jasontsemf/OptiMice/Optimice_V2/Eagle/optiMiceV2/export/board/optiMiceV2_6.png

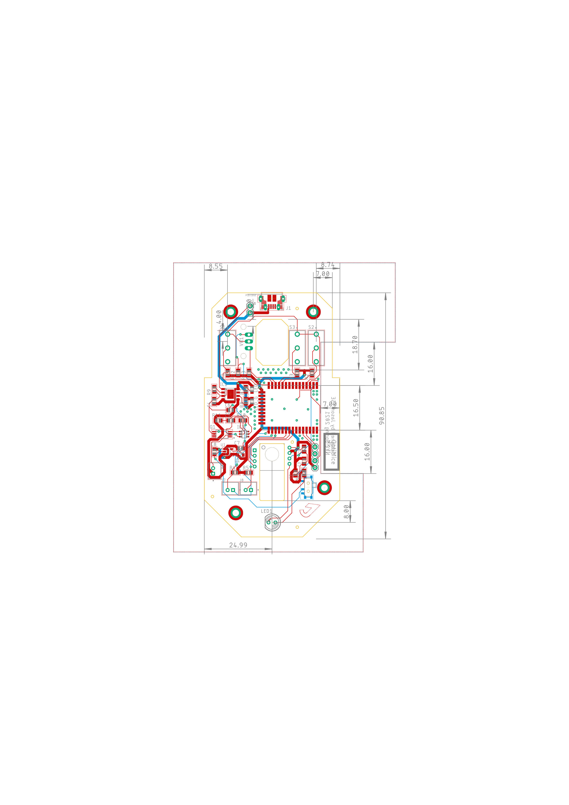
Optimice_V2/Eagle/optiMiceV2/export/board/optiMiceV2_6.png
