jasontsemf/OptiMice/Optimice_V2/Eagle/optiMiceV2/export/board/optiMiceV2_6_bottom.png

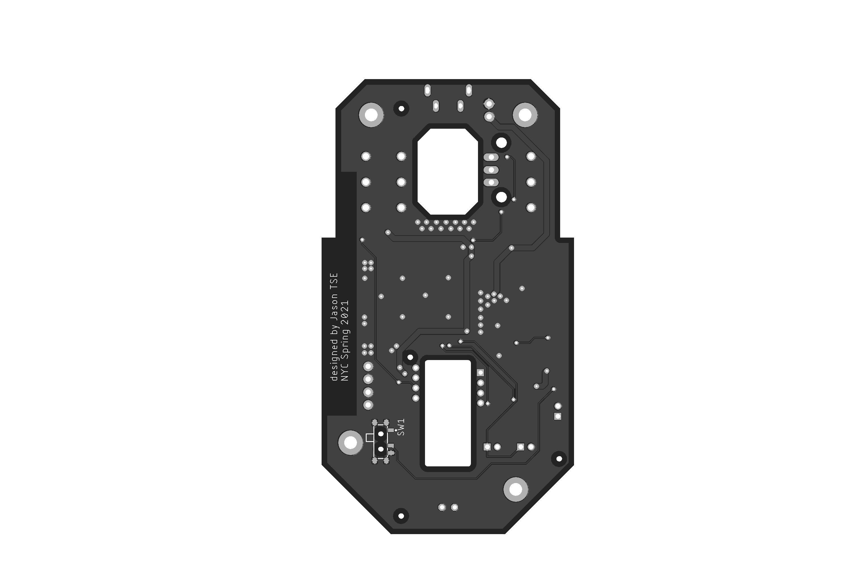
Optimice_V2/Eagle/optiMiceV2/export/board/optiMiceV2_6_bottom.png
