jasontsemf/OptiMice/Optimice_V2/Eagle/optiMiceV2/export/drawing/optiMiceV2_blocktitle.png

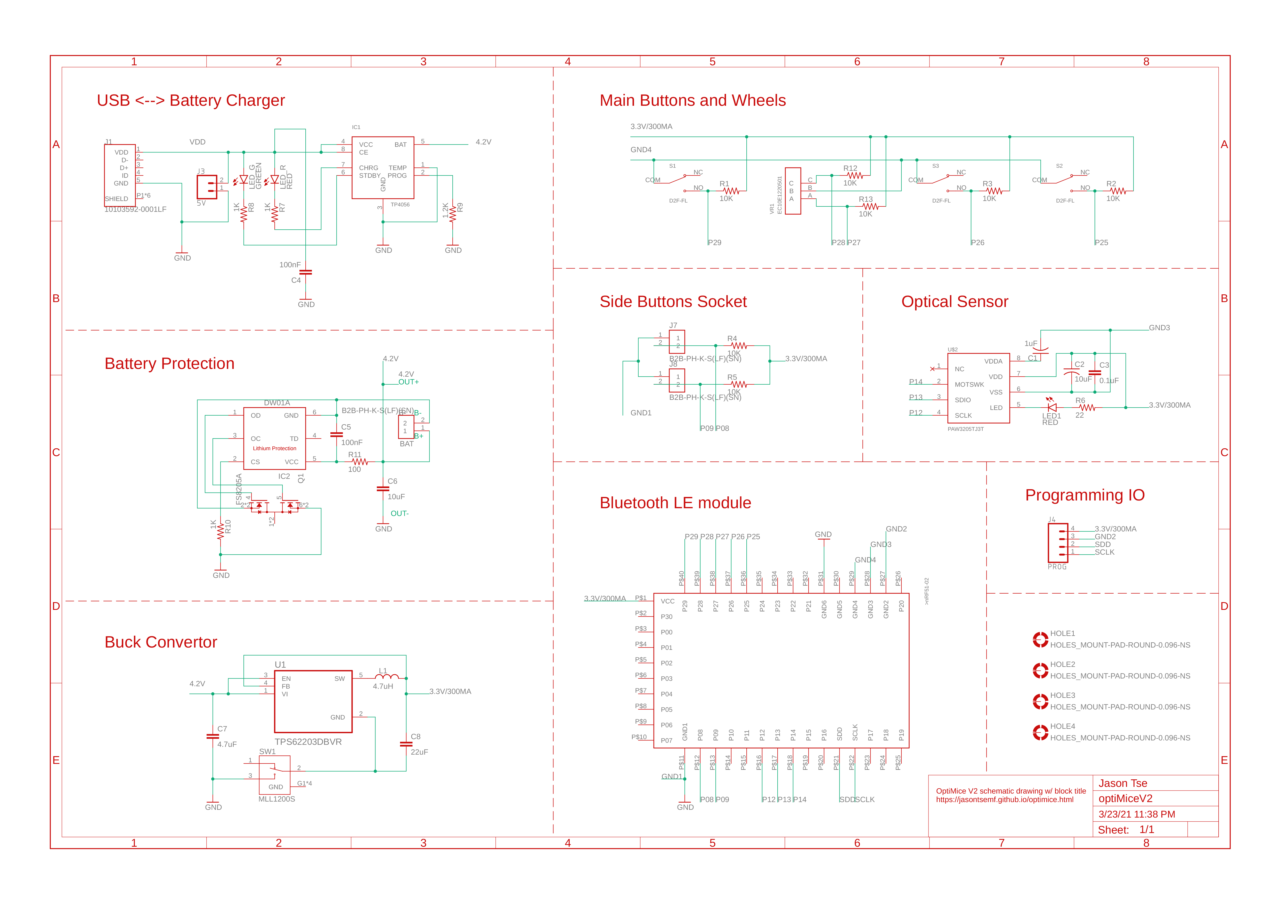
Optimice_V2/Eagle/optiMiceV2/export/drawing/optiMiceV2_blocktitle.png
