jasontsemf/OptiMice/Optimice_V2/Eagle/optiMiceV2/export/drawing/wrong/optiMiceV2_drawing_v0.1.png

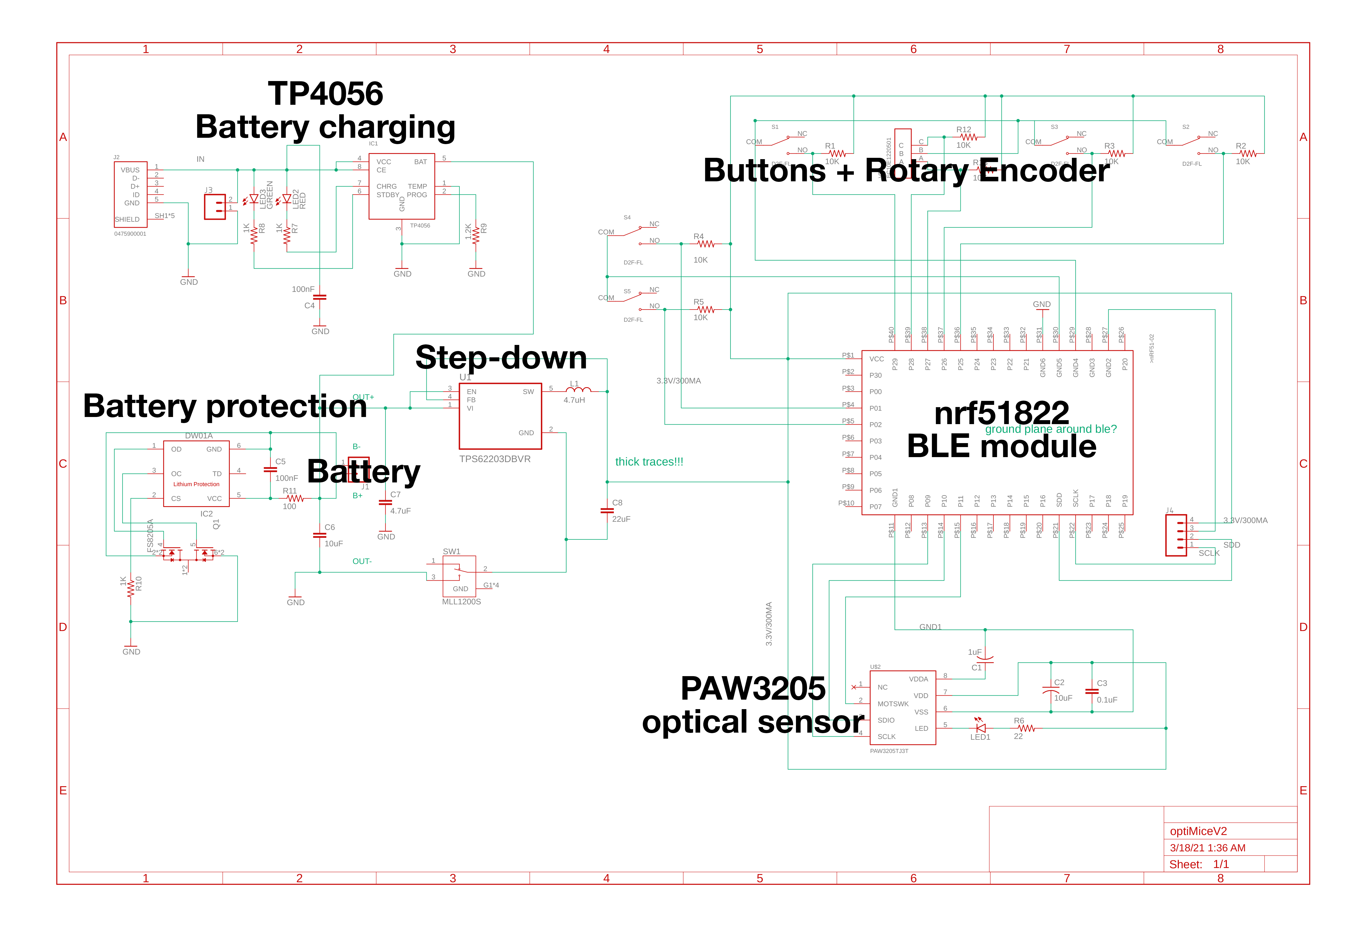
Optimice_V2/Eagle/optiMiceV2/export/drawing/wrong/optiMiceV2_drawing_v0.1.png
