jasontsemf/OptiMice/Optimice_V2/Eagle/optiMiceV2/export/isometric/Layer 2.png

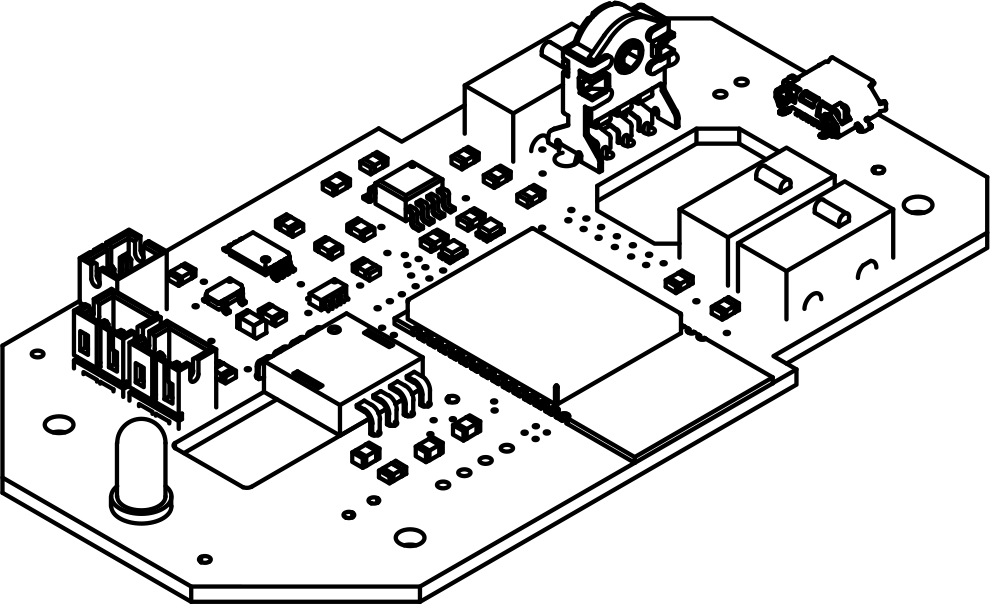
Optimice_V2/Eagle/optiMiceV2/export/isometric/Layer 2.png
