jasontsemf/OptiMice/Optimice_V2/img/_DSC0003.JPG

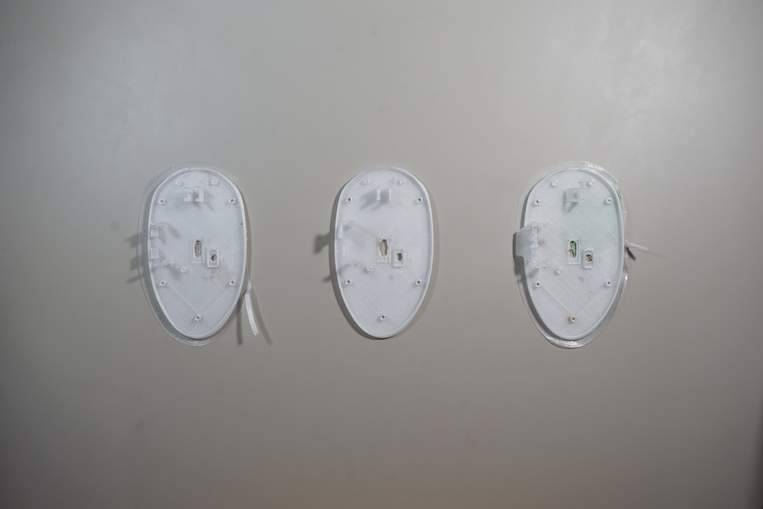
Optimice_V2/img/_DSC0003.JPG
