jasontsemf/OptiMice/Optimice_V2/img/IMG_20210307_201544_508.jpg

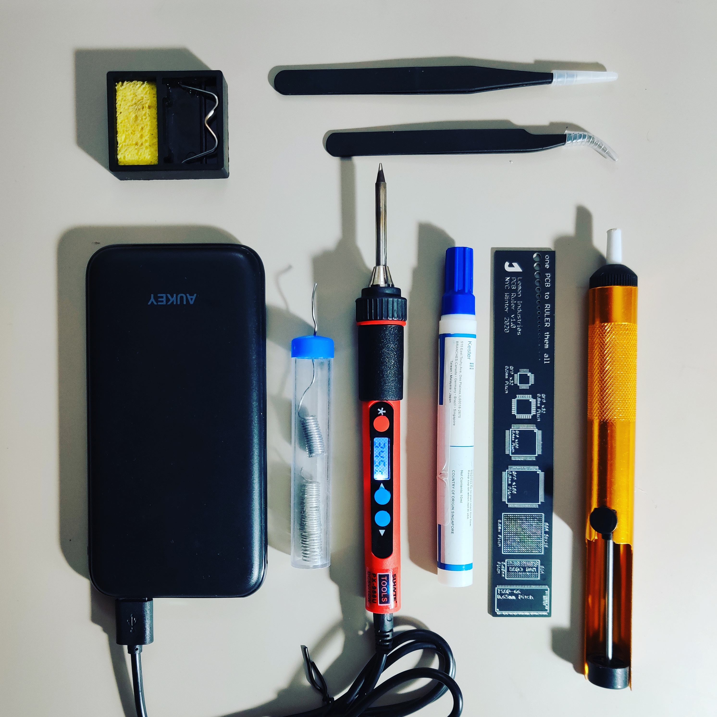
Optimice_V2/img/IMG_20210307_201544_508.jpg
