jasontsemf/OptiMice/Optimice_V2/scan/12310329/_DSC0028.JPG

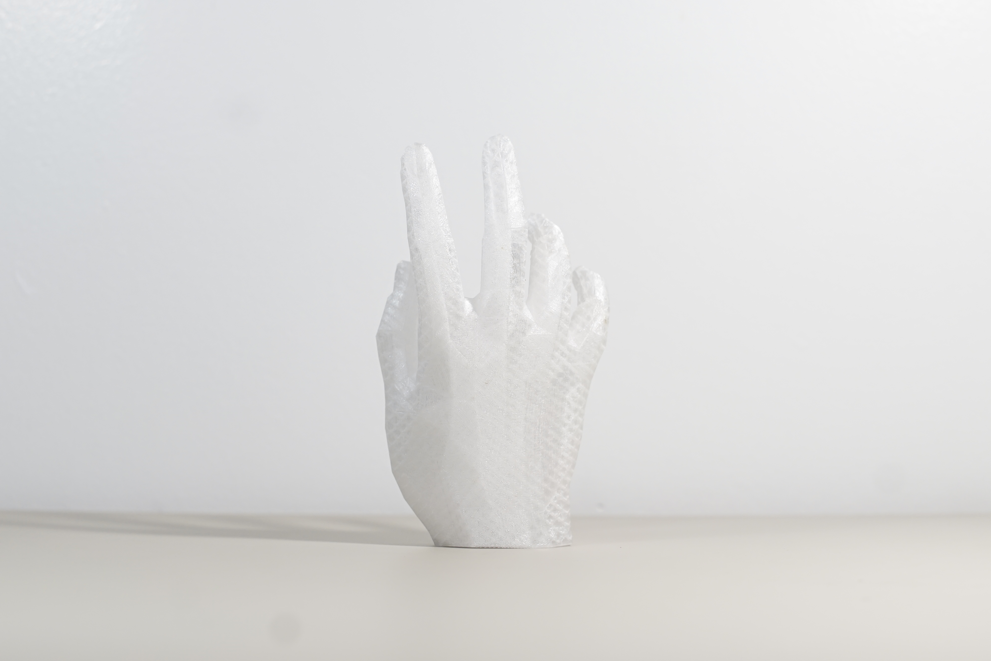
Optimice_V2/scan/12310329/_DSC0028.JPG
