jasontsemf/OptiMice/Optimice_V2/scan/JPEG/reduce size/_DSC0022.jpg

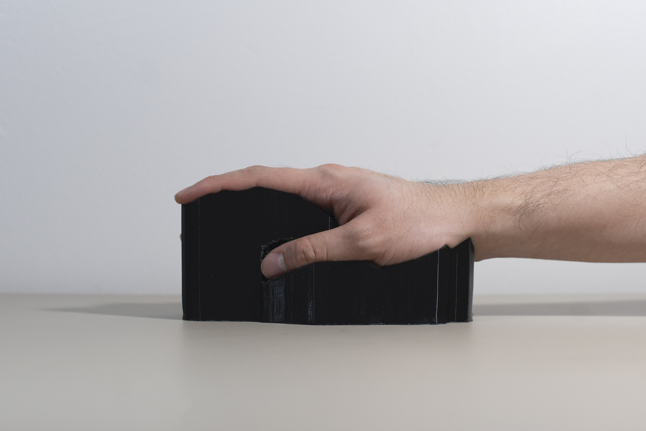
Optimice_V2/scan/JPEG/reduce size/_DSC0022.jpg
