jasontsemf/OptiMice/Optimice_V2/scan/JPEG/reduce size/_DSC0028.jpg

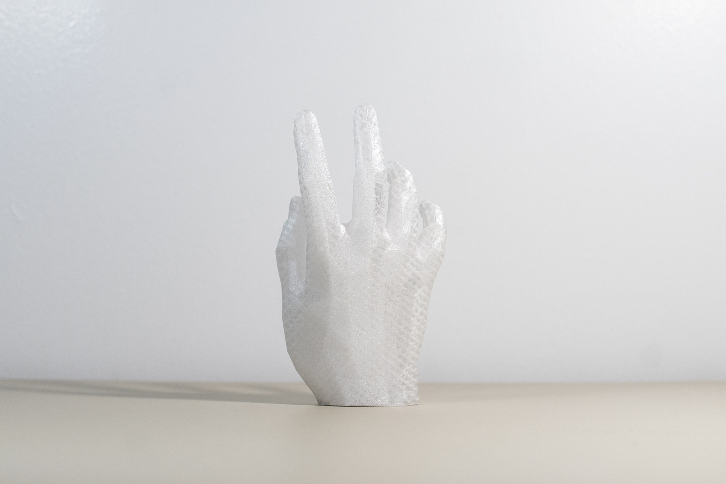
Optimice_V2/scan/JPEG/reduce size/_DSC0028.jpg
