jasontsemf/OptiMice/Optimice_V2/scan/waveshare_button_encoder.jpg

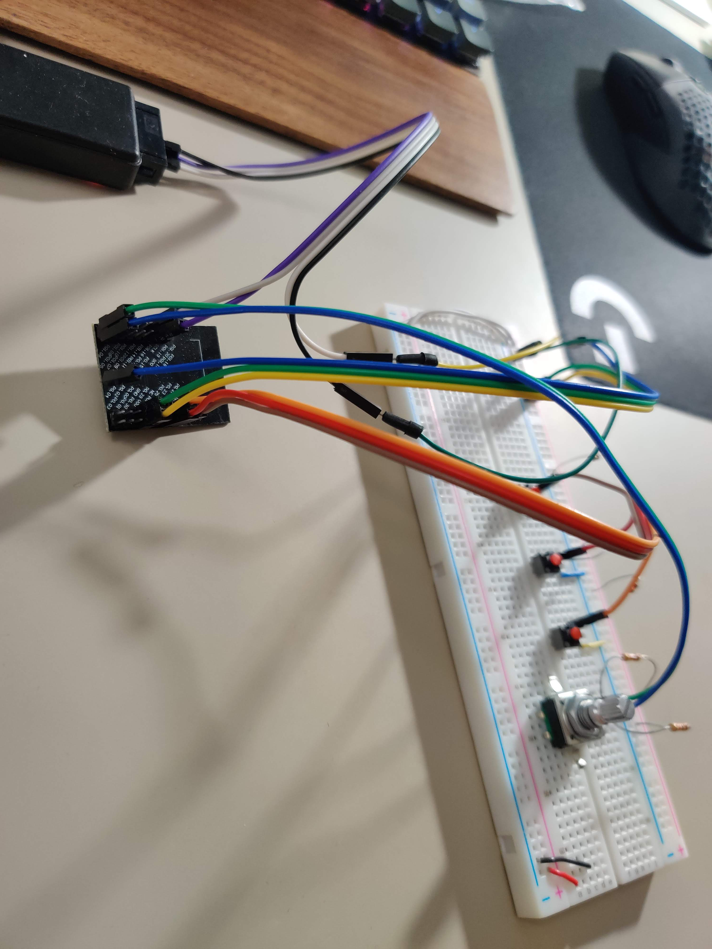
Optimice_V2/scan/waveshare_button_encoder.jpg
