jasontsemf/OptiMice/Optimice_V2/software/I2L-MeshNet_RELEASE/demo/close_to_perfect/input.jpg

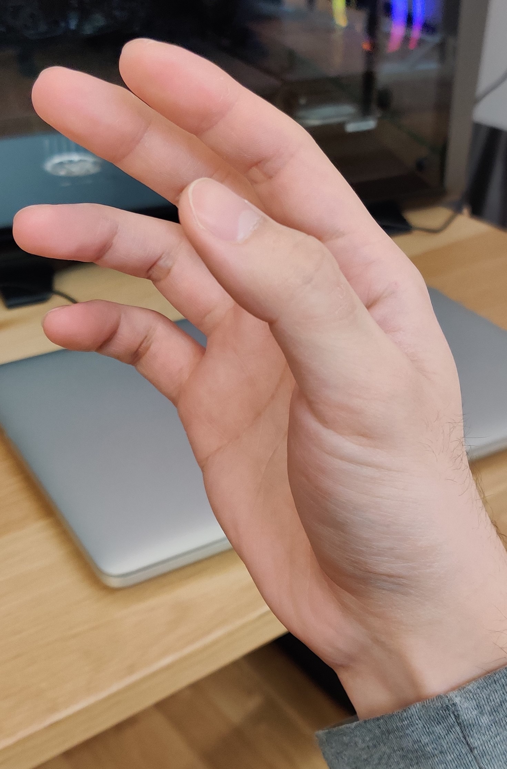
Optimice_V2/software/I2L-MeshNet_RELEASE/demo/close_to_perfect/input.jpg
