jasontsemf/OptiMice/Optimice_V2/software/I2L-MeshNet_RELEASE/demo/close_to_perfect/rendered_mesh_lixel.jpg

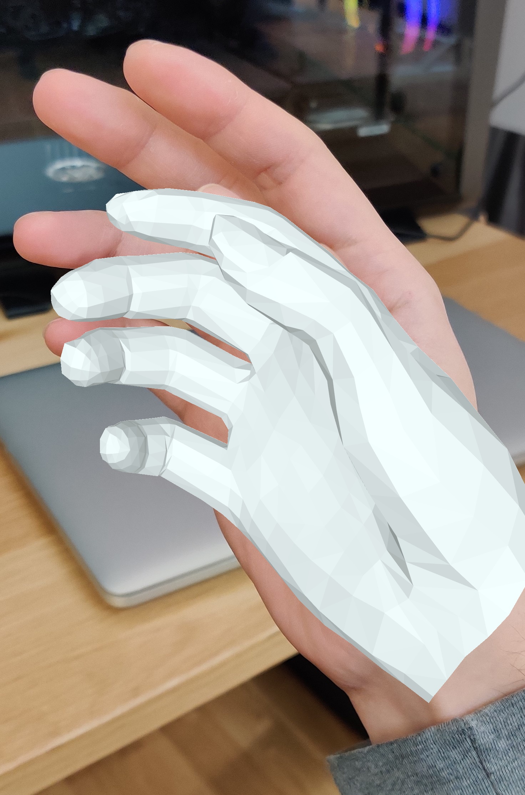
Optimice_V2/software/I2L-MeshNet_RELEASE/demo/close_to_perfect/rendered_mesh_lixel.jpg
