jasontsemf/OptiMice/Optimice_V2/software/I2L-MeshNet_RELEASE/demo/flat/IMG_20210311_142211 - Copy.jpg

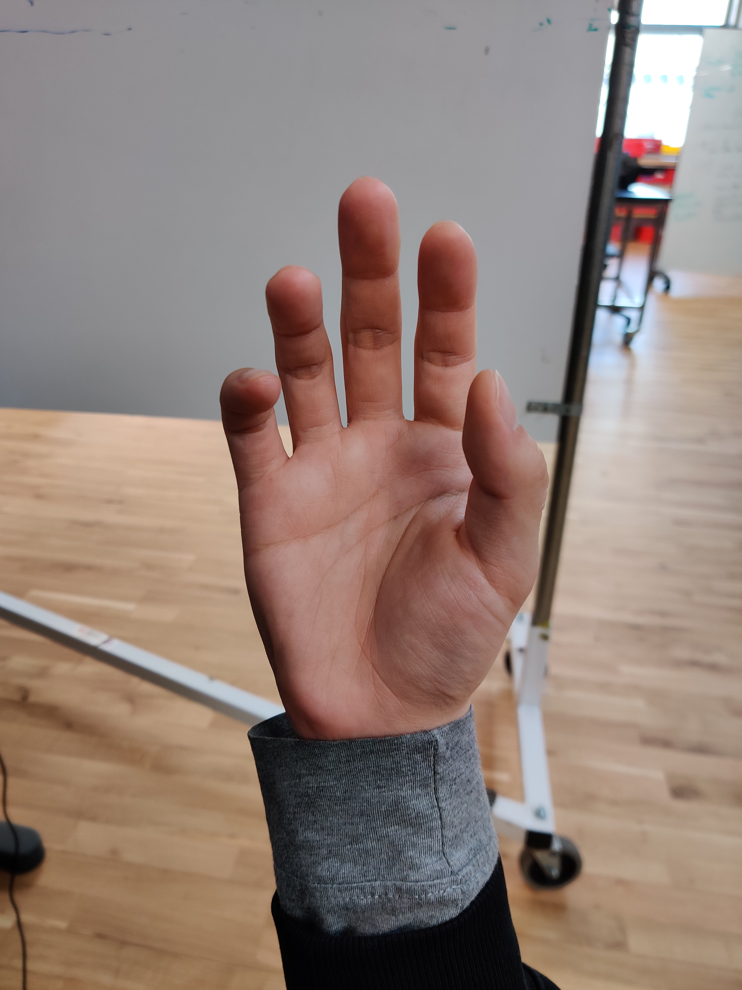
Optimice_V2/software/I2L-MeshNet_RELEASE/demo/flat/IMG_20210311_142211 - Copy.jpg
