jasontsemf/OptiMice/Optimice_V2/software/I2L-MeshNet_RELEASE/demo/flat/input.jpg

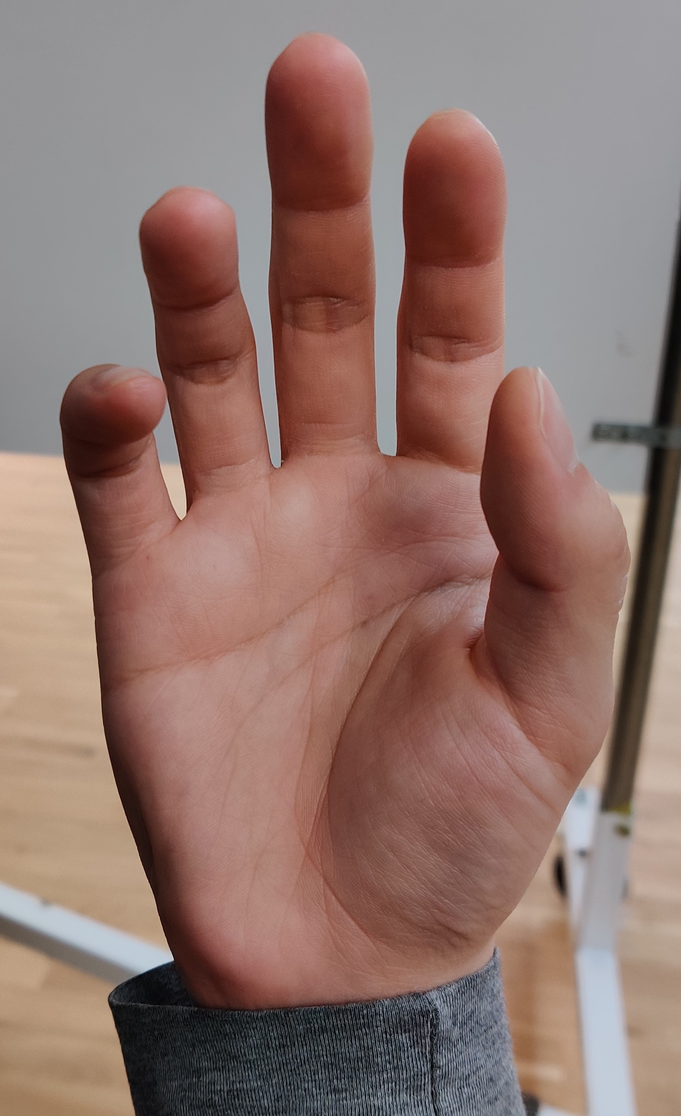
Optimice_V2/software/I2L-MeshNet_RELEASE/demo/flat/input.jpg
