jasontsemf/OptiMice/Optimice_V2/software/I2L-MeshNet_RELEASE/demo/flat/rendered_mesh_lixel.jpg

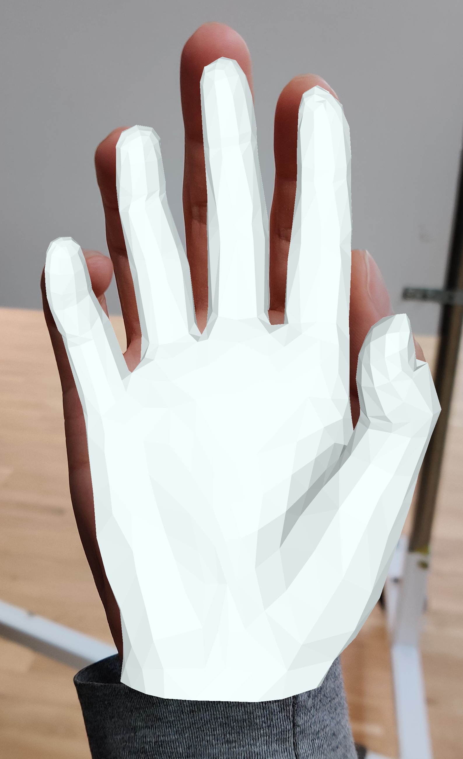
Optimice_V2/software/I2L-MeshNet_RELEASE/demo/flat/rendered_mesh_lixel.jpg
