jasontsemf/OptiMice/Optimice_V2/software/I2L-MeshNet_RELEASE/demo/quite_good/input.jpg

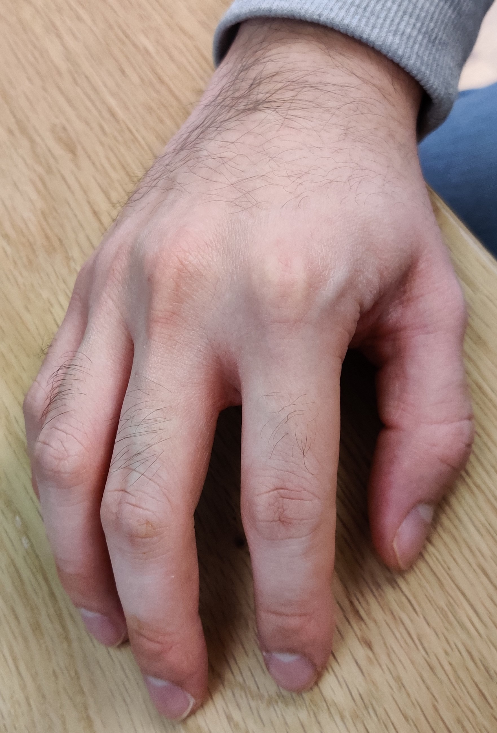
Optimice_V2/software/I2L-MeshNet_RELEASE/demo/quite_good/input.jpg
