jasontsemf/OptiMice/Optimice_V2/software/I2L-MeshNet_RELEASE/demo/quite_good/rendered_mesh_lixel.jpg

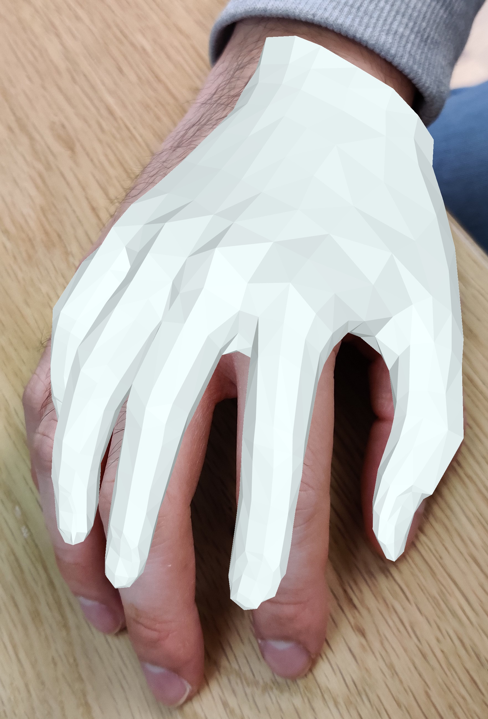
Optimice_V2/software/I2L-MeshNet_RELEASE/demo/quite_good/rendered_mesh_lixel.jpg
