jasontsemf/OptiMice/V2/documentation/1x/roadmapArtboard 1.png

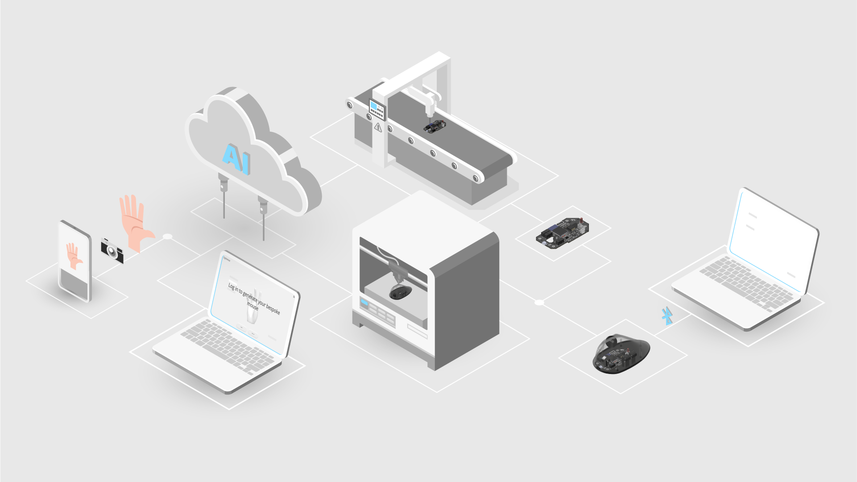
V2/documentation/1x/roadmapArtboard 1.png
