jasontsemf/OptiMice/V2/documentation/pcb.png

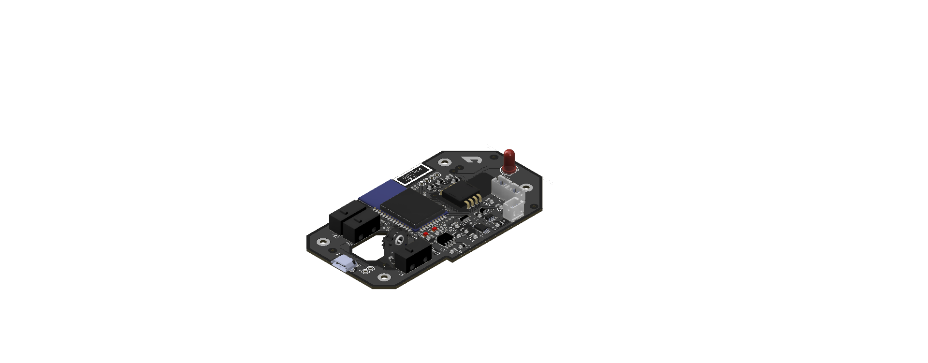
V2/documentation/pcb.png
