jasontsemf/OptiMice/V2/documentation/whole-shell.png

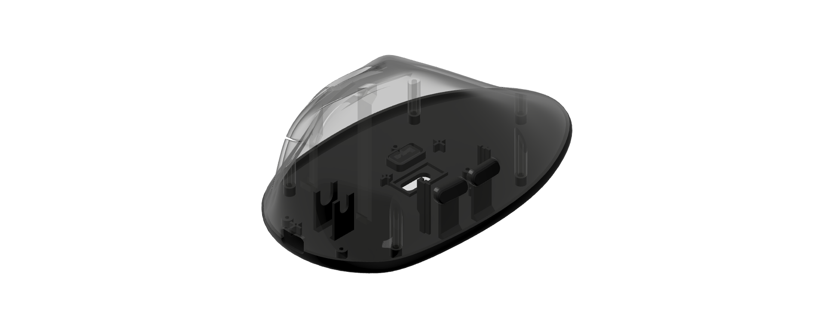
V2/documentation/whole-shell.png
