jasontsemf/OptiMice/V2/rendering/2a3aa41a-aebc-47f1-b04d-556dffb02604.PNG

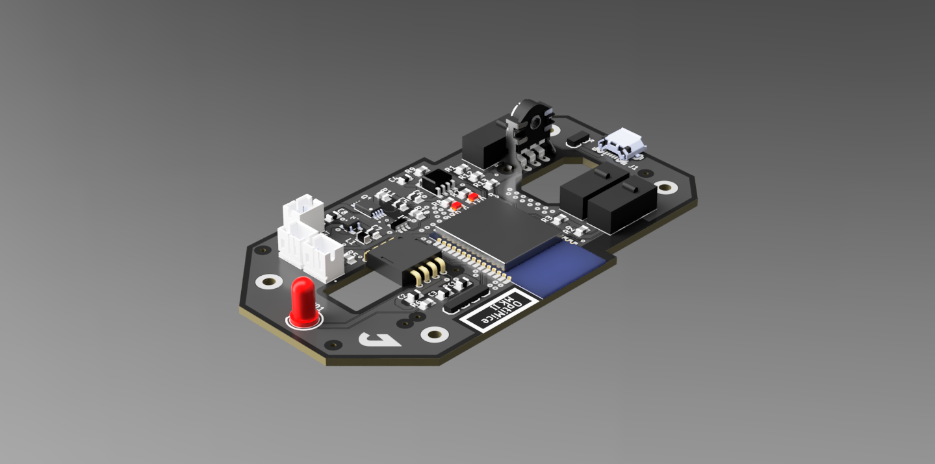
V2/rendering/2a3aa41a-aebc-47f1-b04d-556dffb02604.PNG
