jasontsemf/OptiMice/V2/rendering/3b4c1e57-d749-43ba-b765-23364f0c6340.PNG

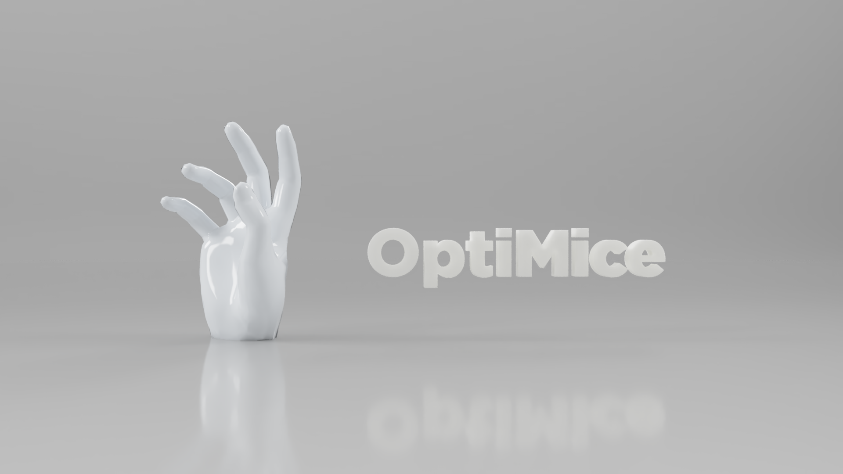
V2/rendering/3b4c1e57-d749-43ba-b765-23364f0c6340.PNG
