jasontsemf/OptiMice/V2/rendering/3eef2709-c4ba-487f-86fd-f23eb43f0d84.PNG

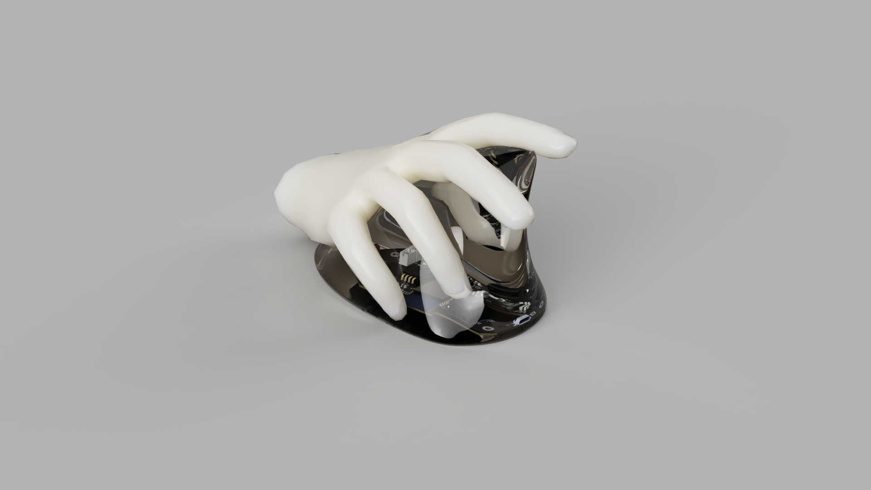
V2/rendering/3eef2709-c4ba-487f-86fd-f23eb43f0d84.PNG
