jasontsemf/OptiMice/V2/rendering/7bf40a13-bb4c-4bf1-a939-91cfa63c3272.PNG

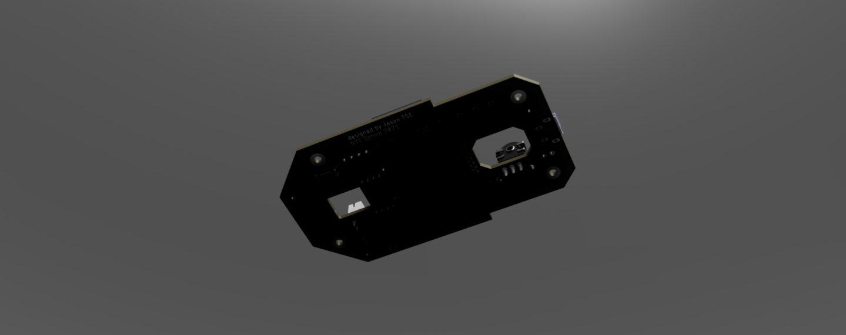
V2/rendering/7bf40a13-bb4c-4bf1-a939-91cfa63c3272.PNG
