jasontsemf/OptiMice/V2/rendering/7fbafc41-bdba-4dc0-bb99-120f7759c94d.PNG

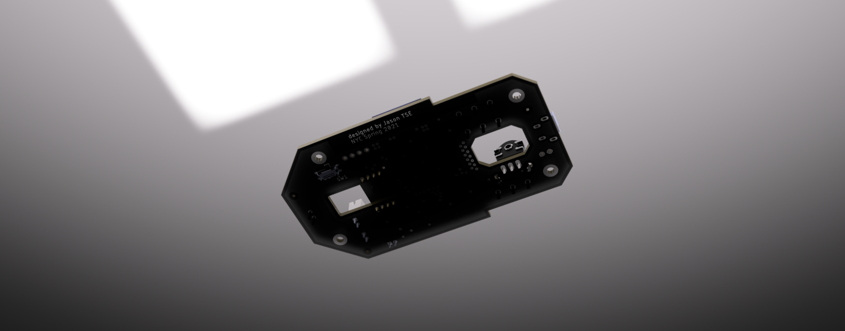
V2/rendering/7fbafc41-bdba-4dc0-bb99-120f7759c94d.PNG
