jasontsemf/OptiMice/V2/rendering/53cbd0f5-f580-4500-9d3a-d8ba97ffdd0f.PNG

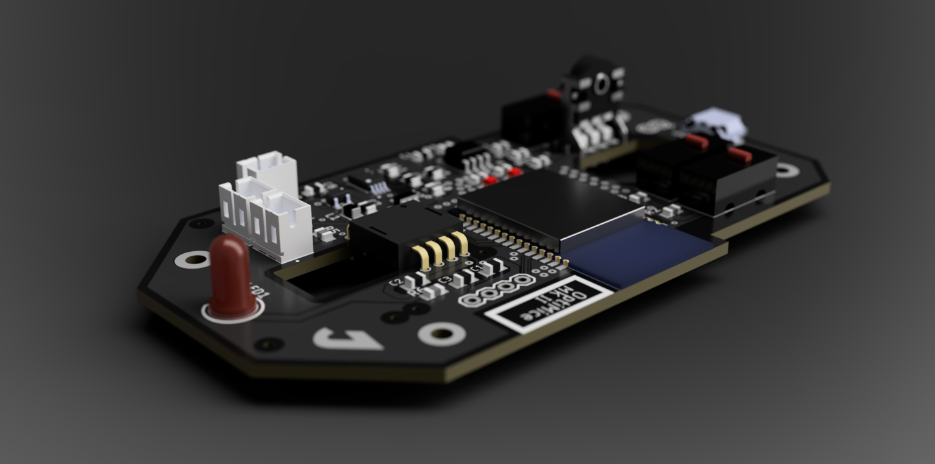
V2/rendering/53cbd0f5-f580-4500-9d3a-d8ba97ffdd0f.PNG
