jasontsemf/OptiMice/V2/rendering/24855e21-a8eb-4672-9b0f-5984bc3ee39a.PNG

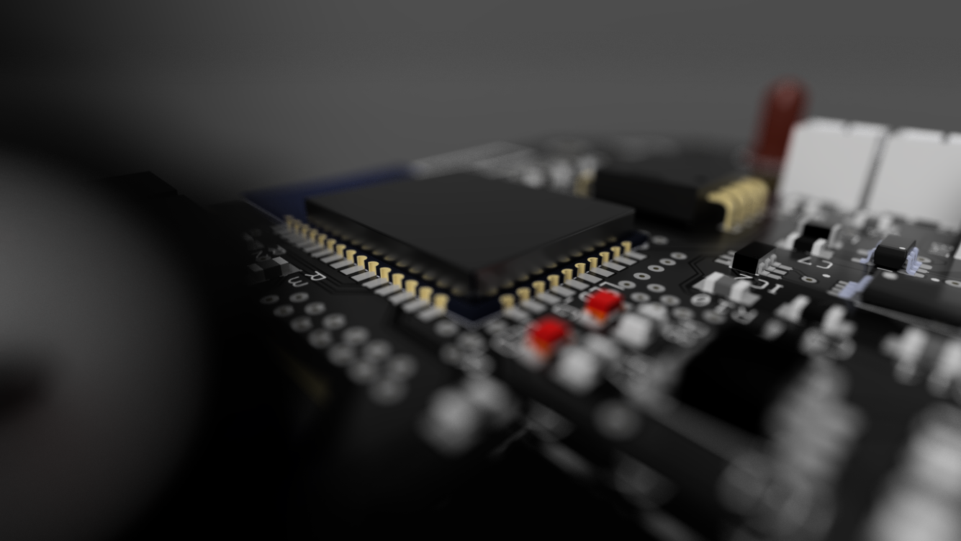
V2/rendering/24855e21-a8eb-4672-9b0f-5984bc3ee39a.PNG
