jasontsemf/OptiMice/V2/rendering/913427af-ce87-4a00-b79b-c7be0dc9a041.PNG

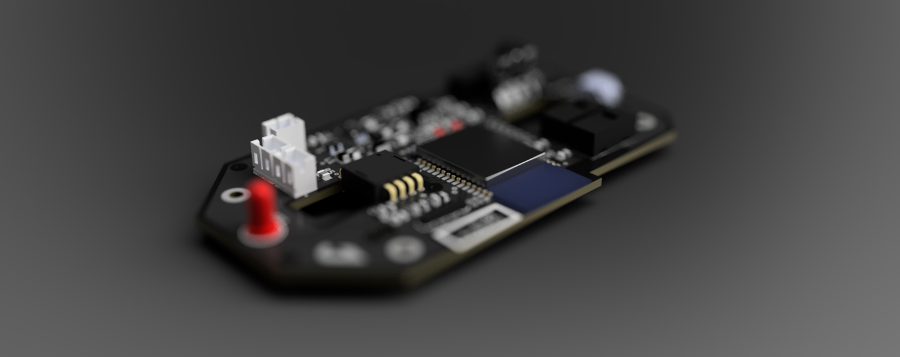
V2/rendering/913427af-ce87-4a00-b79b-c7be0dc9a041.PNG
