jasontsemf/OptiMice/V2/rendering/22556311-6284-45e4-bcc1-b64f9aabeae4.PNG

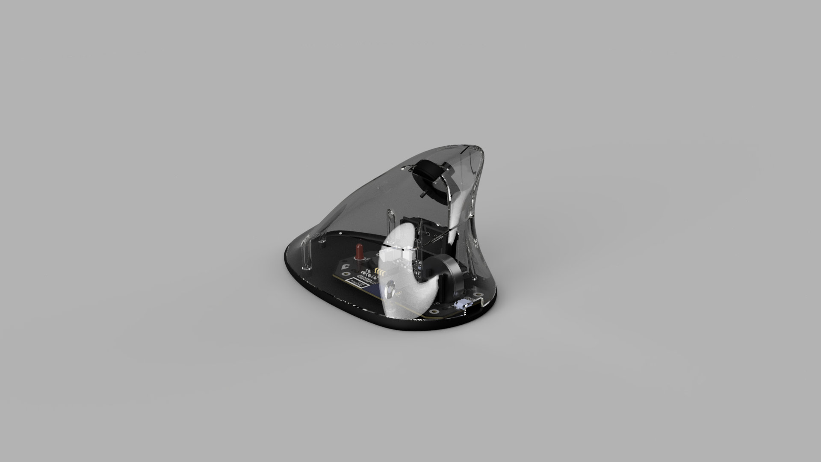
V2/rendering/22556311-6284-45e4-bcc1-b64f9aabeae4.PNG
