jasontsemf/OptiMice/V2/rendering/d13697d3-9024-4b81-a56f-18733b45574d.PNG

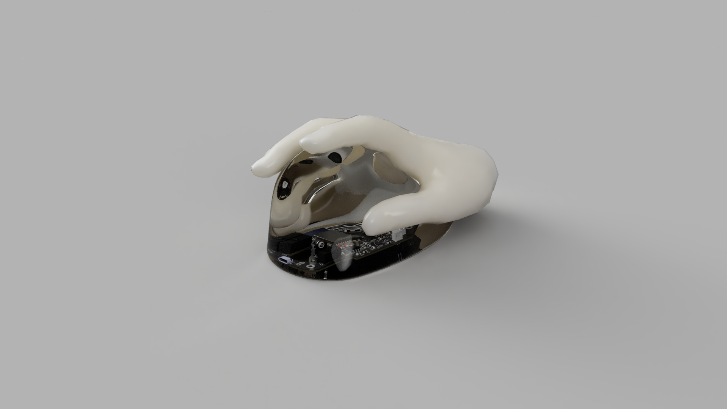
V2/rendering/d13697d3-9024-4b81-a56f-18733b45574d.PNG
