jasontsemf/OptiMice/V2/rendering/f5711cdf-db0f-4792-b860-c40e9feee94d.PNG

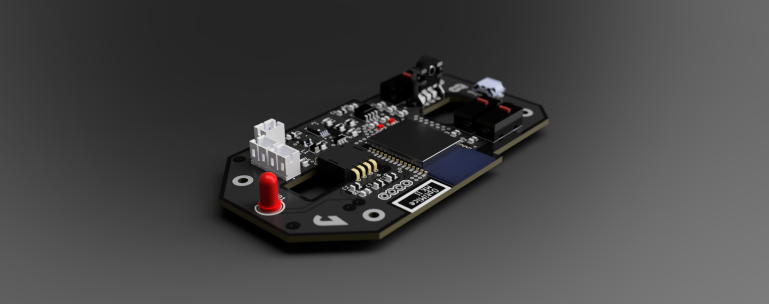
V2/rendering/f5711cdf-db0f-4792-b860-c40e9feee94d.PNG
