jasontsemf/OptiMice/V2/rendering/fd1c8e8d-d576-4ce3-8ad7-112644cd6fff.PNG

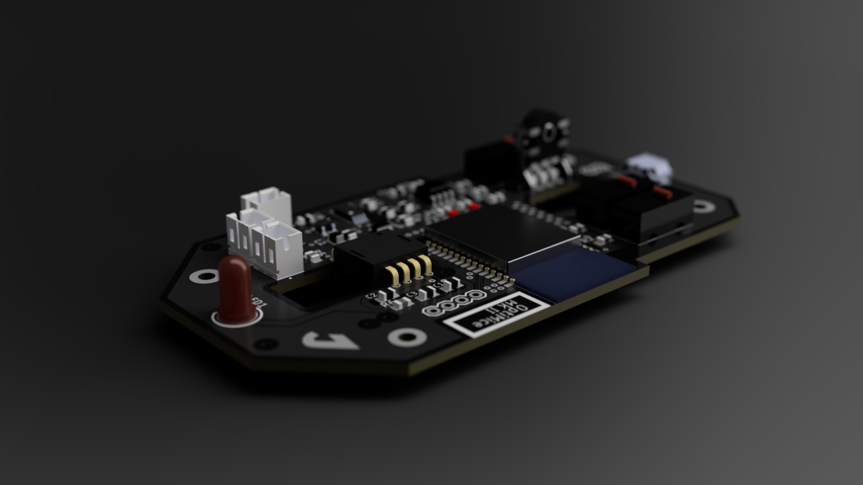
V2/rendering/fd1c8e8d-d576-4ce3-8ad7-112644cd6fff.PNG
