jasontsemf/OptiMice/V2/rendering/jason_hand_half_minimal_2021-Apr-18_06-10-25AM-000_CustomizedView14442562156 copy.png

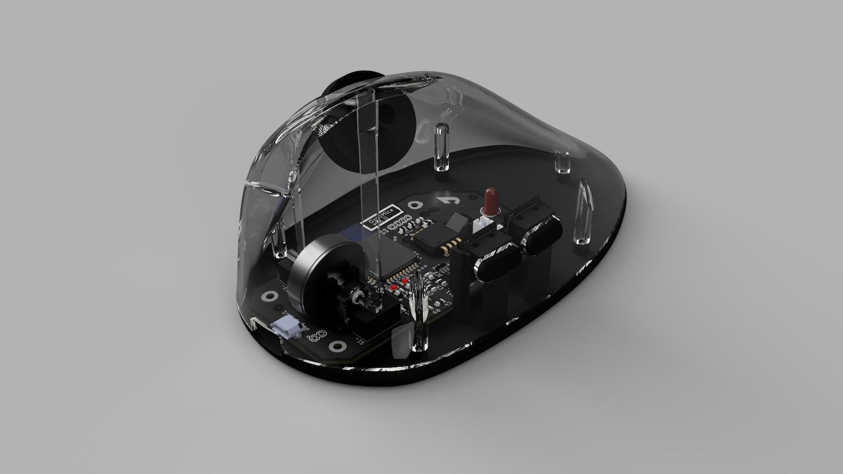
V2/rendering/jason_hand_half_minimal_2021-Apr-18_06-10-25AM-000_CustomizedView14442562156 copy.png
