jasontsemf/OptiMice/V2/rendering/jason_hand_half_minimal_2021-Apr-18_06-13-18AM-000_CustomizedView42542229077.png

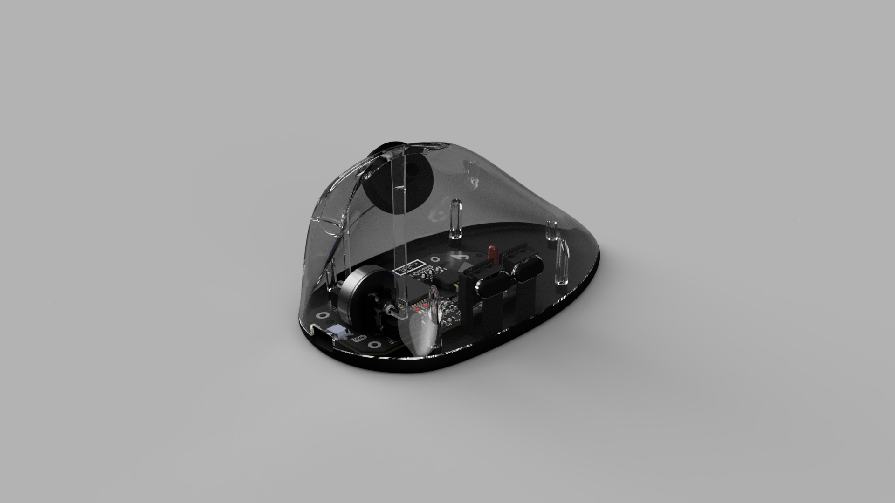
V2/rendering/jason_hand_half_minimal_2021-Apr-18_06-13-18AM-000_CustomizedView42542229077.png
