jasontsemf/OptiMice/V2/rendering/jason_hand_half_minimal_2021-Apr-18_06-59-04AM-000_CustomizedView21048777239 copy.png

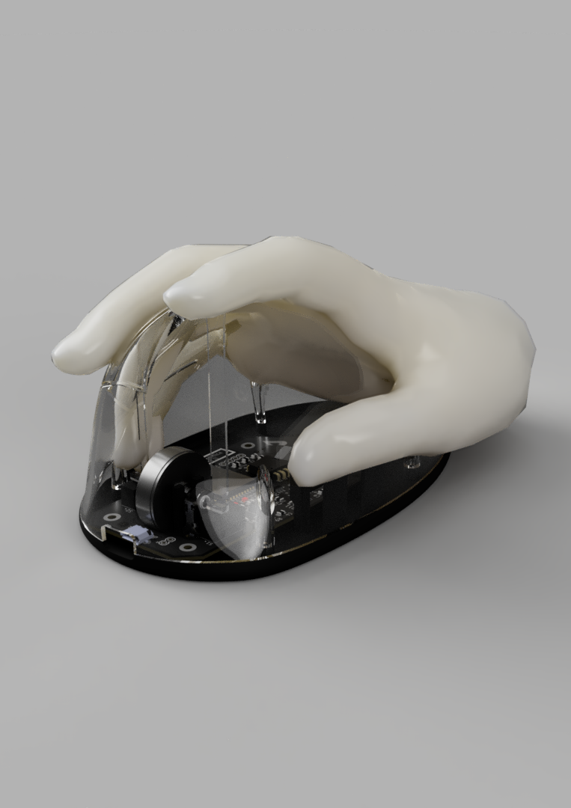
V2/rendering/jason_hand_half_minimal_2021-Apr-18_06-59-04AM-000_CustomizedView21048777239 copy.png
