jasontsemf/OptiMice/V2/rendering/title copy.png

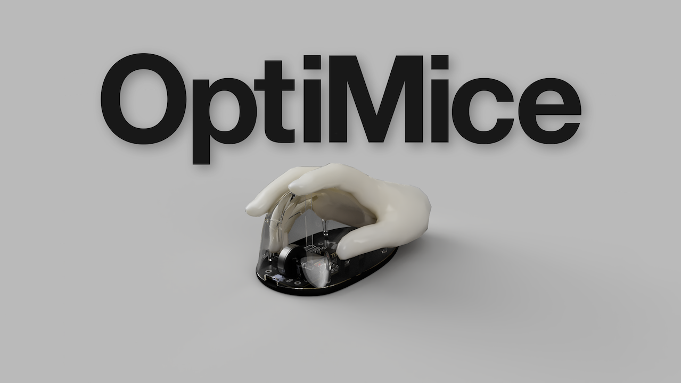
V2/rendering/title copy.png
