jasontsemf/OptiMice/V2/rendering/title_white.png

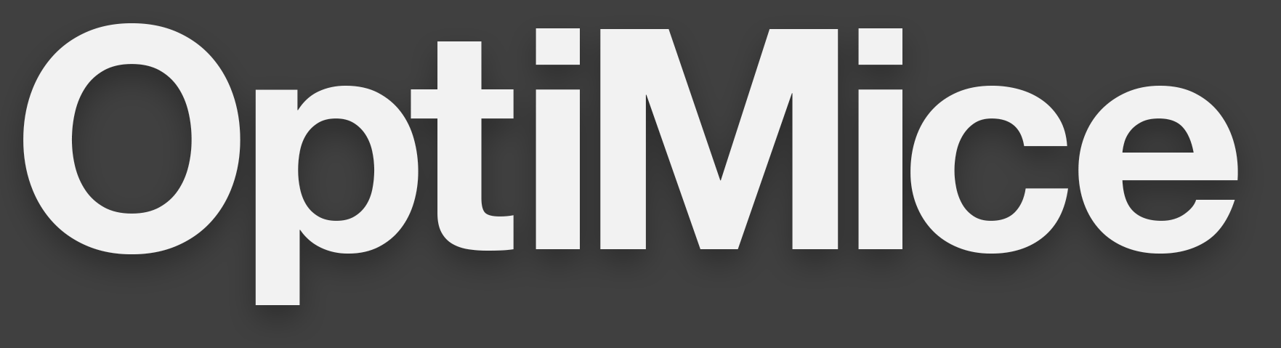
V2/rendering/title_white.png
