jasontsemf/OptiMice/Optimice_V2/software/my_hand/jason_hand_1_closed.obj

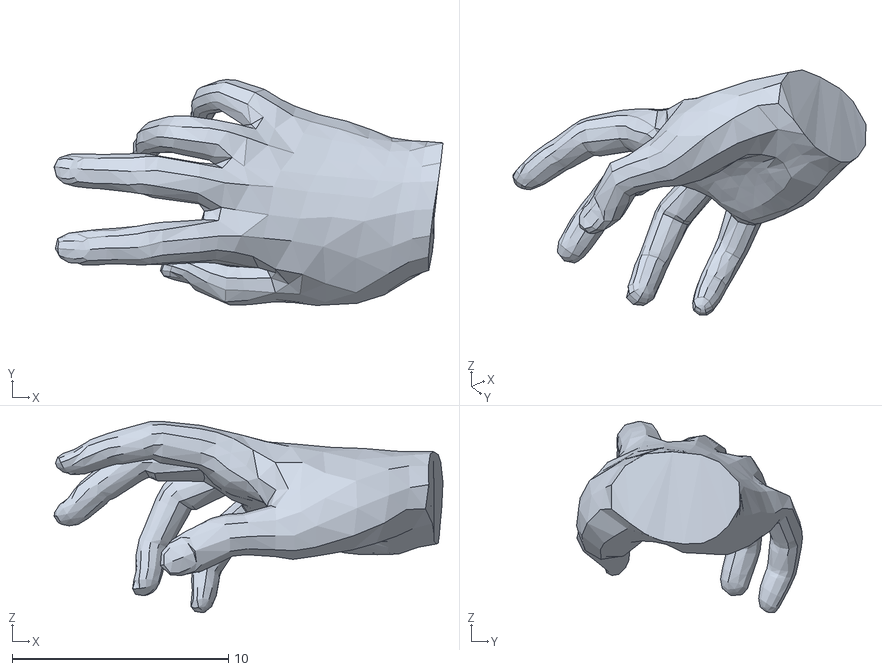
[picture p85: CAD file, 2022-03-21]
Optimice_V2/software/my_hand/jason_hand_1_closed.obj
18.0 x 10.5 x 8.85
