jasontsemf/OptiMice/Optimice_V2/software/my_hand/second_try/jason_hand_1.obj

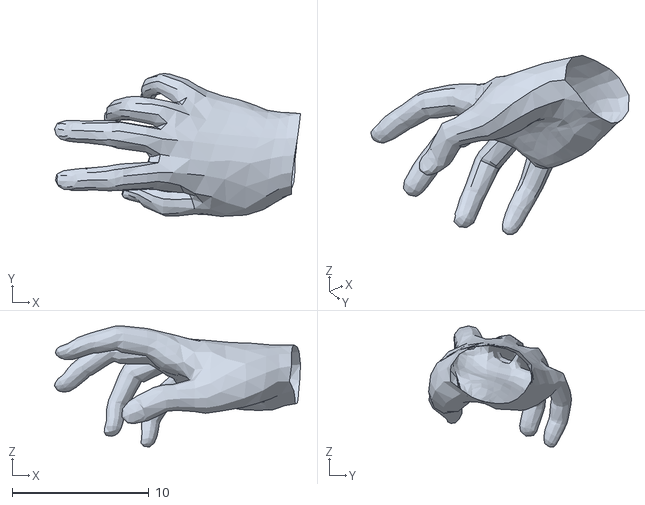
[picture p86: CAD file, 2022-03-21]
Optimice_V2/software/my_hand/second_try/jason_hand_1.obj
18.0 x 10.5 x 8.85
