jasontsemf/OptiMice/Optimice_V2/software/my_hand/second_try/jason_hand_half_minimal.obj

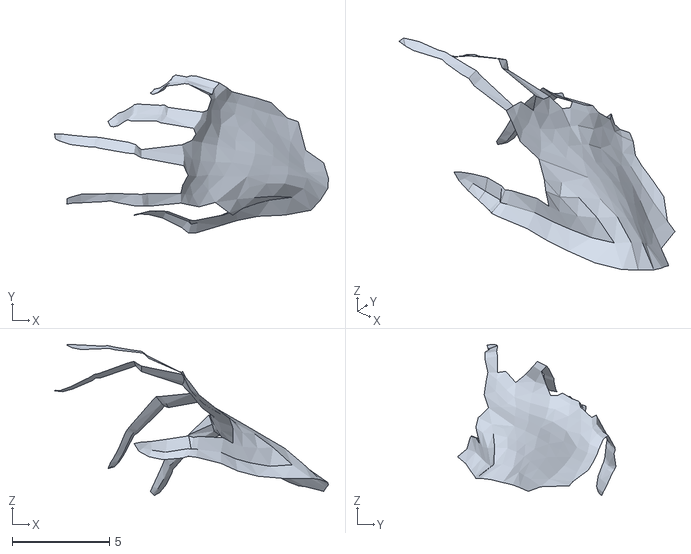
[picture p87: CAD file, 2022-03-21]
Optimice_V2/software/my_hand/second_try/jason_hand_half_minimal.obj
14.1 x 8.11 x 7.76
