jasontsemf/OptiMice/Optimice_V2/software/my_hand/second_try/hand_reorient.obj

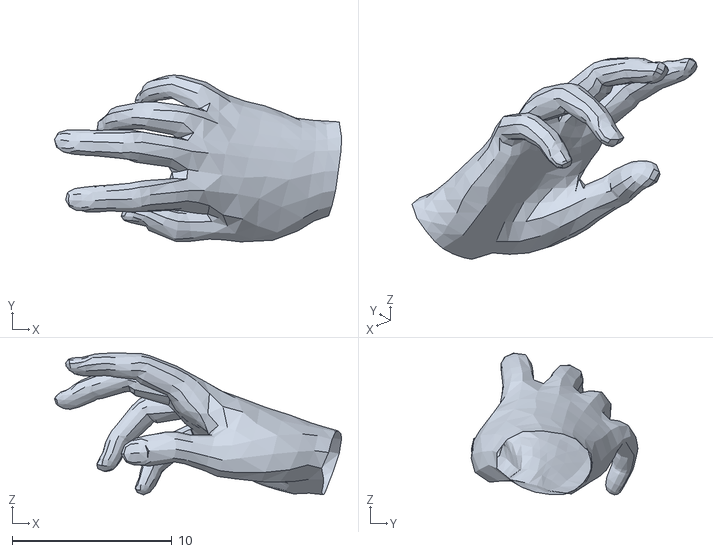
[picture p88: CAD file, 2022-03-21]
Optimice_V2/software/my_hand/second_try/hand_reorient.obj
18.0 x 10.5 x 8.89
