jasontsemf/OptiMice/Optimice_V2/Eagle/optiMiceV2/export/board/optiMiceV2_5.pdf

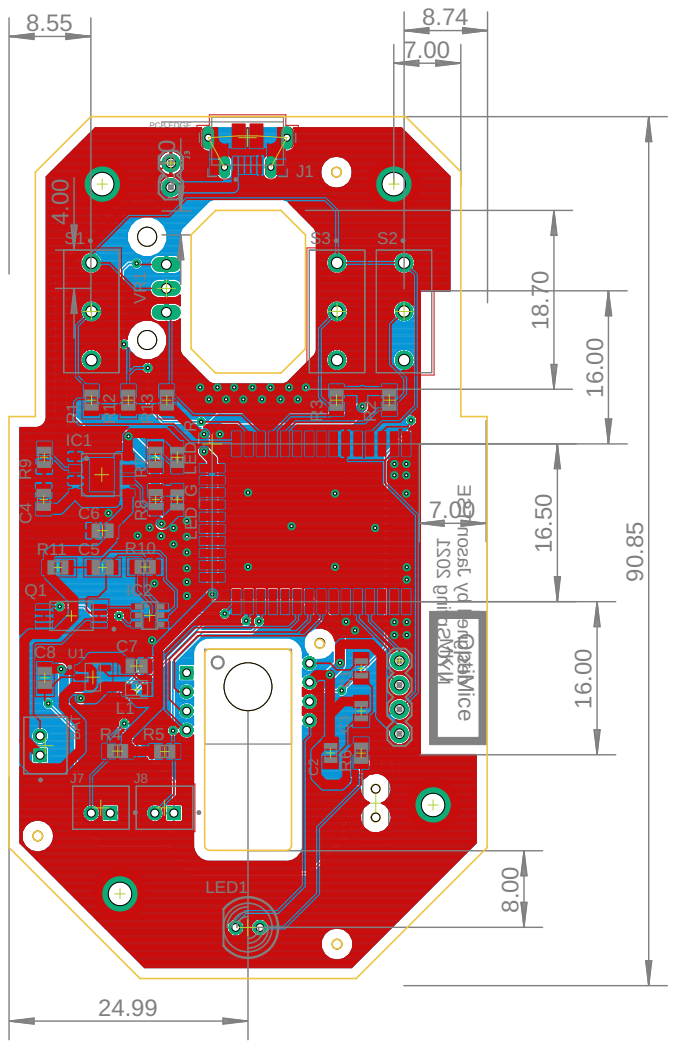
[picture p98: page 1]

designed by Jason TSE NYC Spring 2021 OptiMice MK II 18.70
