jasontsemf/OptiMice/V2/Arduino/HID_test/HID_test.ino

// Copyright (c) Sandeep Mistry. All rights reserved.
// Licensed under the MIT license. See LICENSE file in the project root for full license information.

// Import libraries (BLEPeripheral depends on SPI)
#include <SPI.h>
#include <BLEHIDPeripheral.h>
#include <BLEMouse.h>
#include <BLEKeyboard.h>
#include <BLEMultimedia.h>
#include <BLESystemControl.h>

// define pins (varies per shield/board)
#define BLE_REQ   6
#define BLE_RDY   7
#define BLE_RST   4

BLEHIDPeripheral bleHID = BLEHIDPeripheral(BLE_REQ, BLE_RDY, BLE_RST);
BLEMouse bleMouse;
BLEKeyboard bleKeyboard;
BLEMultimedia bleMultimedia;
BLESystemControl bleSystemControl;

void setup() {
  Serial.begin(9600);
#if defined (__AVR_ATmega32U4__)
  while(!Serial);
#endif

  // clears bond data on every boot
  bleHID.clearBondStoreData();

   bleHID.setDeviceName("Arduino BLE HID jason");
//  bleHID.setAppearance(961);

  bleHID.setLocalName("HID");

//  bleHID.addHID(bleMouse);
//  bleHID.addHID(bleKeyboard);
  bleHID.addHID(bleMultimedia);
//  bleHID.addHID(bleSystemControl);

  bleHID.begin();

  Serial.println(F("BLE HID"));
}

void loop() {
  BLECentral central = bleHID.central();

  if (central) {
    // central connected to peripheral
    Serial.print(F("Connected to central: "));
    Serial.println(central.address());

    while (bleHID.connected()) {
      if (Serial.available() > 0) {
        Serial.read();

//        bleMouse.move(100, 100, 0);
//        bleKeyboard.press(KEYCODE_A);
        bleMultimedia.write(MMKEY_VOL_UP);
//        bleSystemControl.write(SYSCTRLKEY_POWER);
      }
    }

    // central disconnected
    Serial.print(F("Disconnected from central: "));
    Serial.println(central.address());
  }
}
