jasontsemf/OptiMice/Optimice_V2/img/IMG_20210208_031154.jpg

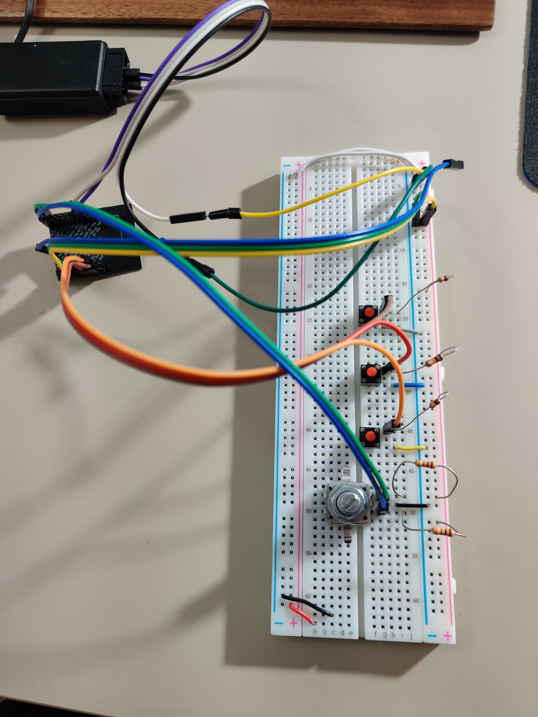
Optimice_V2/img/IMG_20210208_031154.jpg
