jasontsemf/OptiMice/Optimice_V2/img/IMG_20210304_193242.jpg

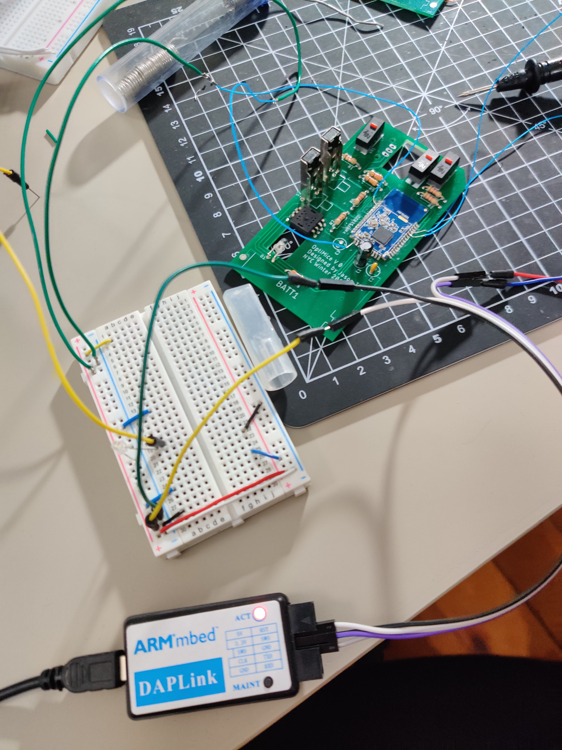
Optimice_V2/img/IMG_20210304_193242.jpg
