jasontsemf/OptiMice/Optimice_V2/software/I2L-MeshNet_RELEASE/demo/close_to_perfect/IMG_20210311_130806 - Copy.jpg

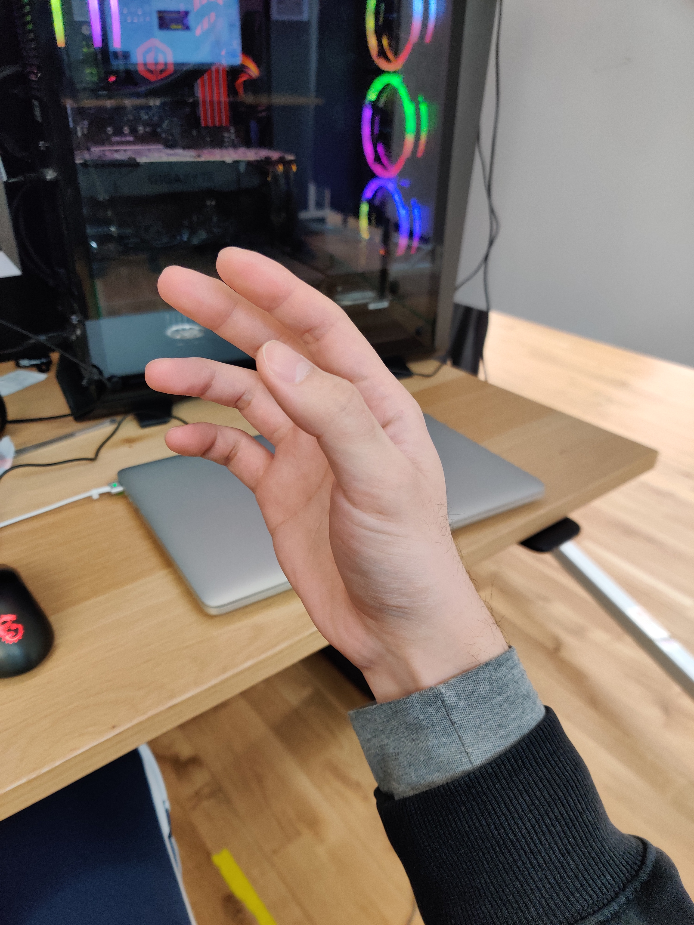
Optimice_V2/software/I2L-MeshNet_RELEASE/demo/close_to_perfect/IMG_20210311_130806 - Copy.jpg
