jasontsemf/OptiMice/Optimice_V2/software/I2L-MeshNet_RELEASE/demo/quite_good/input - Copy.jpg

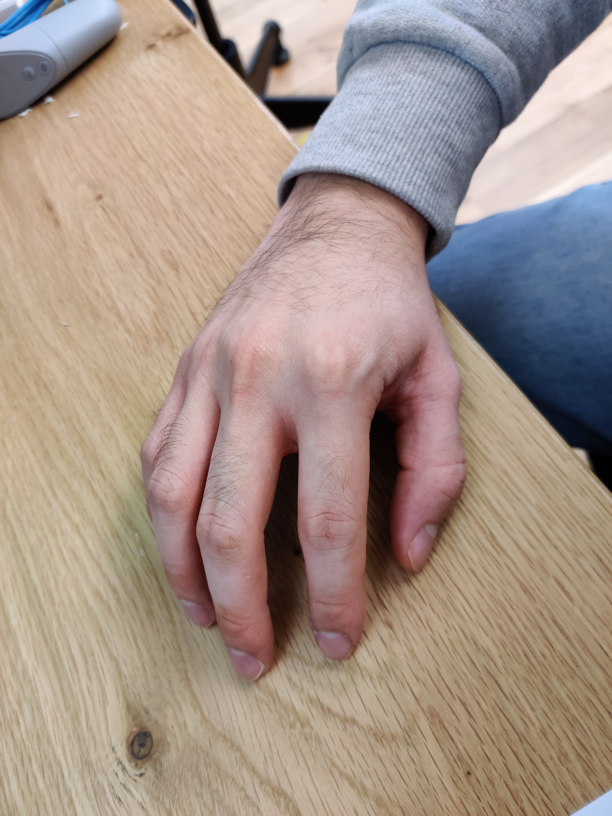
Optimice_V2/software/I2L-MeshNet_RELEASE/demo/quite_good/input - Copy.jpg
